AbinR6/TS-Air-Quality-Monitor/AirMonitor/03_Traceability/TRACEABILITY.md

# Traceability & Verification Framework

## 1. Overview
The Air Monitor engineering project maintains end-to-end traceability across all engineering artifacts. Every functional requirement, hardware design choice, firmware module, and software utility connects directly from operational specifications to hardware schematics, firmware drivers, software tools, and verification test suites.

```text
OPERATIONAL REQUIREMENTS
           |
           v
SYSTEM ARCHITECTURE & HARDWARE SCHEMATIC
           |
           v
FIRMWARE DRIVERS & PIPELINE ENGINE
           |
           v
SOFTWARE TOOLS & TELEMETRY INGESTION
           |
           v
VERIFICATION & TEST SUITES
```

---

## 2. Traceability Matrix Structure

1. **Requirements Traceability**: [`03_Traceability/requirements_traceability.md`](file:///c:/Users/abina/Downloads/STM32%20Project/AirMonitor/03_Traceability/requirements_traceability.md)
   - Maps operational, environmental, hardware, and networking requirements to implementing subsystems and verification methods.
2. **Hardware Traceability Matrix**: [`03_Traceability/hardware_traceability_matrix.md`](file:///c:/Users/abina/Downloads/STM32%20Project/AirMonitor/03_Traceability/hardware_traceability_matrix.md)
   - Traces hardware components from system requirements to BOM line items, KiCad schematics, PCB footprints, and 3D CAD assets.
3. **Firmware Traceability Matrix**: [`03_Traceability/firmware_traceability_matrix.md`](file:///c:/Users/abina/Downloads/STM32%20Project/AirMonitor/03_Traceability/firmware_traceability_matrix.md)
   - Traces firmware modules, FreeRTOS tasks, peripheral drivers, and state machines to hardware contracts and functional tests.
4. **Software Traceability Matrix**: [`03_Traceability/software_traceability_matrix.md`](file:///c:/Users/abina/Downloads/STM32%20Project/AirMonitor/03_Traceability/software_traceability_matrix.md)
   - Traces host tools, device simulation, and telemetry decoders to the IoT telemetry data model.
5. **Component Qualification Register**: [`03_Traceability/uncertainty_register.md`](file:///c:/Users/abina/Downloads/STM32%20Project/AirMonitor/03_Traceability/uncertainty_register.md)
   - Documents candidate component evaluations, tolerance analyses, alternative sourcing, and qualification criteria.
6. **Engineering Decision Log**: [`03_Traceability/engineering_decision_log.md`](file:///c:/Users/abina/Downloads/STM32%20Project/AirMonitor/03_Traceability/engineering_decision_log.md)
   - Architectural Decision Records (ADRs) capturing design rationales for system partitioning, bus architectures, and data structures.
7. **Hardware Inspection to Implementation Matrix**: [`03_Traceability/evidence_to_implementation_matrix.md`](file:///c:/Users/abina/Downloads/STM32%20Project/AirMonitor/03_Traceability/evidence_to_implementation_matrix.md)
   - Correlates physical board inspection markers to schematic symbols, layout features, and firmware pin assignments.
