AbinR6/TS-Air-Quality-Monitor/AirMonitor/01_Evidence/annotated/E001_annotated.png

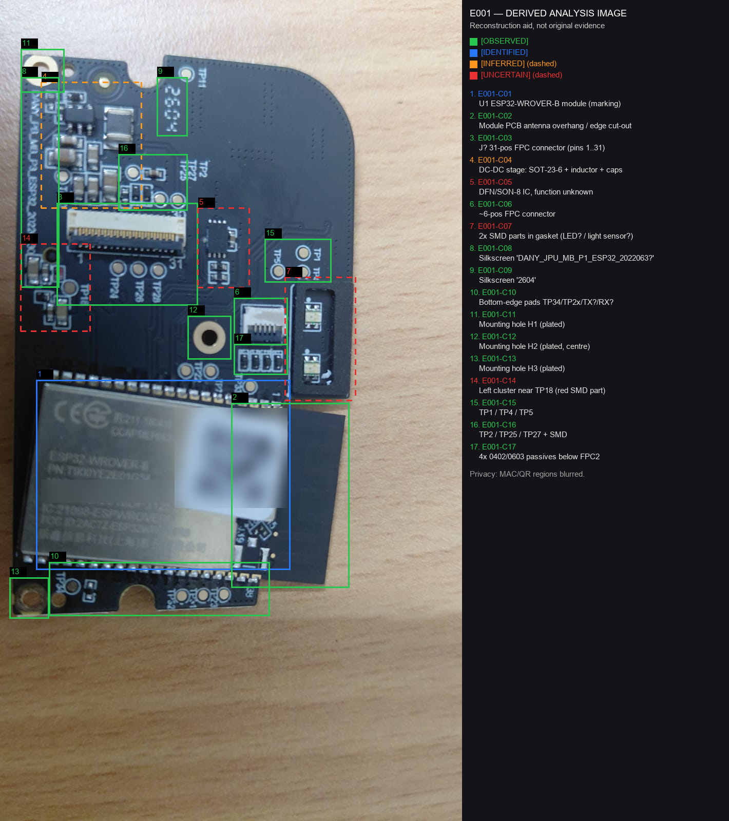
AirMonitor/01_Evidence/annotated/E001_annotated.png
