AbinR6/TS-Air-Quality-Monitor/AirMonitor/01_Evidence/annotated/E003_annotated.png

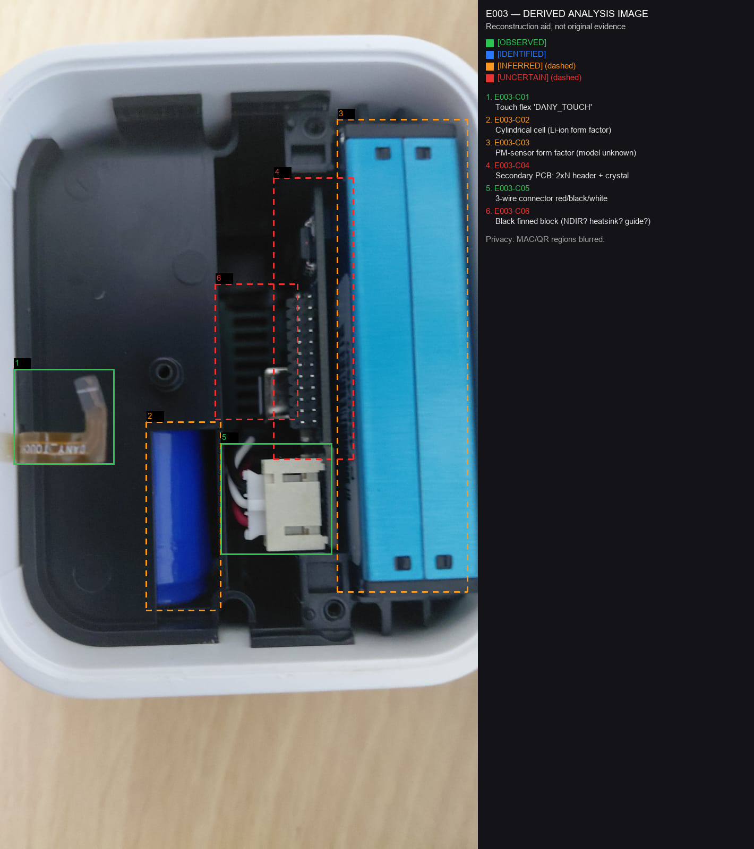
AirMonitor/01_Evidence/annotated/E003_annotated.png
