AbinR6/TS-Air-Quality-Monitor/AirMonitor/01_Evidence/annotated/E004_annotated.png

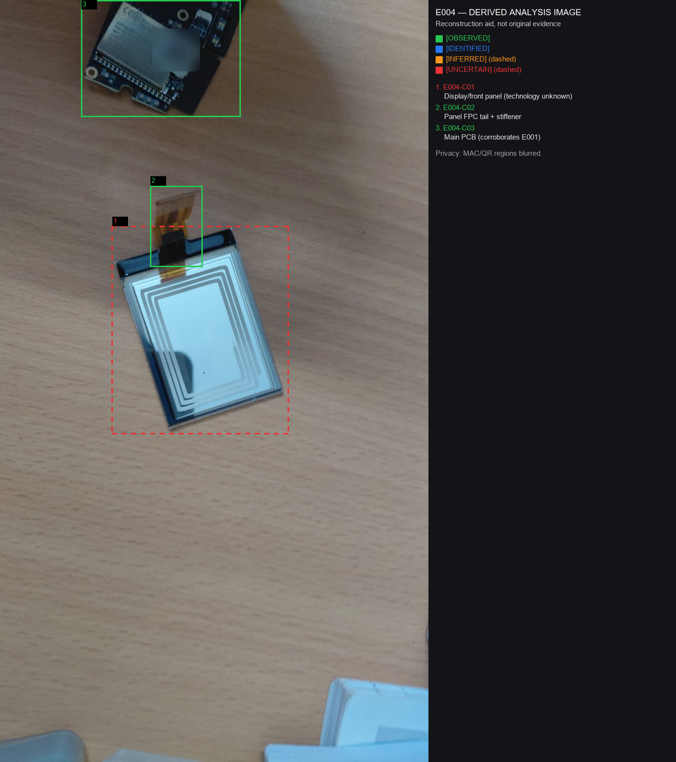
AirMonitor/01_Evidence/annotated/E004_annotated.png
