AbinR6/TS-Air-Quality-Monitor/AirMonitor/01_Evidence/crops/E001-C07.png

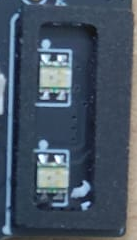
AirMonitor/01_Evidence/crops/E001-C07.png
