AbinR6/TS-Air-Quality-Monitor/AirMonitor/01_Evidence/crops/E001-C14.png

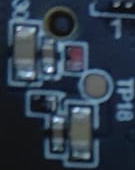
AirMonitor/01_Evidence/crops/E001-C14.png
