AbinR6/TS-Air-Quality-Monitor/AirMonitor/01_Evidence/crops/E001-C16_enh4x.png

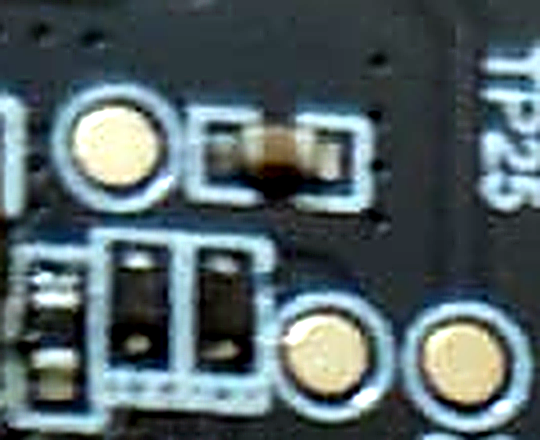
AirMonitor/01_Evidence/crops/E001-C16_enh4x.png
