AbinR6/TS-Air-Quality-Monitor/AirMonitor/01_Evidence/crops/E003-C03.png

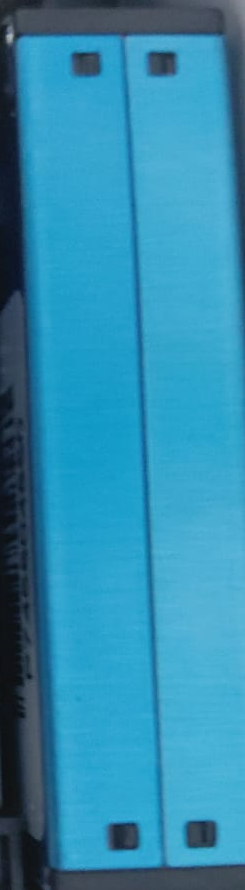
AirMonitor/01_Evidence/crops/E003-C03.png
