AbinR6/TS-Air-Quality-Monitor/AirMonitor/01_Evidence/crops/E003-C03_enh4x.png

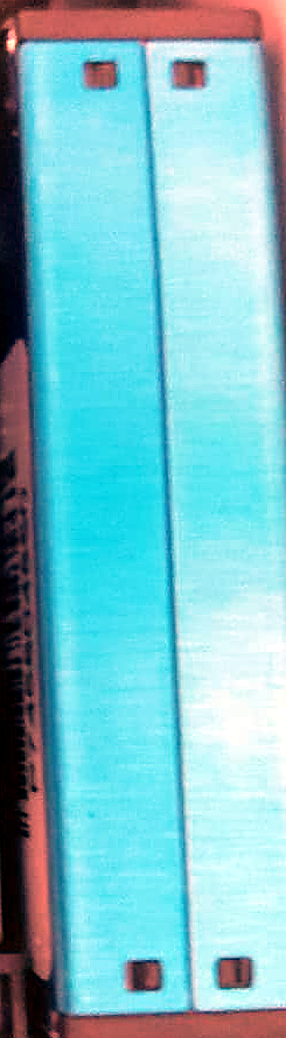
AirMonitor/01_Evidence/crops/E003-C03_enh4x.png
