AbinR6/TS-Air-Quality-Monitor/AirMonitor/01_Evidence/crops/E003-C04.png

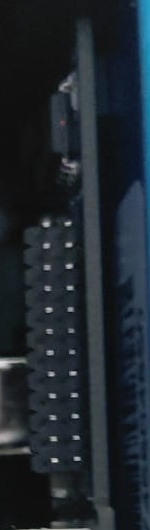
AirMonitor/01_Evidence/crops/E003-C04.png
