AbinR6/TS-Air-Quality-Monitor/AirMonitor/01_Evidence/crops/E004-C01.png

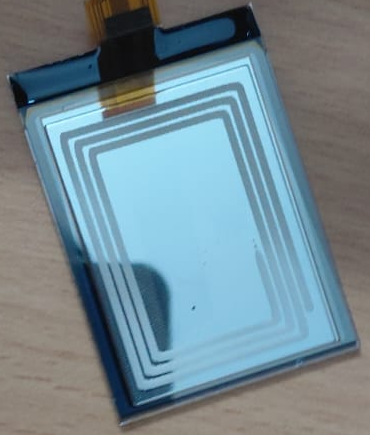
AirMonitor/01_Evidence/crops/E004-C01.png
