AbinR6/TS-Air-Quality-Monitor/AirMonitor/01_Evidence/crops/E004-C02_enh4x.png

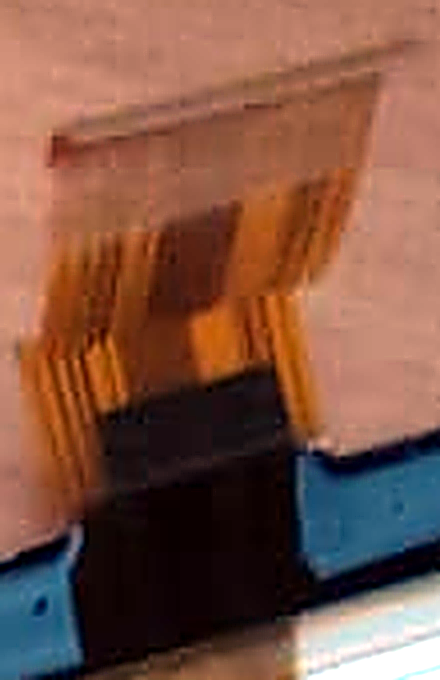
AirMonitor/01_Evidence/crops/E004-C02_enh4x.png
